dauthanhtrung/Arduino-Simple-Phone/CODE TEST/KeyPad/KeyPad.ino

#include <Keypad.h>

const byte ROWS = 4; 
const byte COLS = 4; 

char hexaKeys[ROWS][COLS] = {
  {'1', '2', '3', 'A'},
  {'4', '5', '6', 'B'},
  {'7', '8', '9', 'C'},
  {'*', '0', '#', 'D'}
};

byte rowPins[ROWS] = {9, 10, 11, 12}; 
byte colPins[COLS] = {A0, A1, A2, A3}; 

Keypad key = Keypad(makeKeymap(hexaKeys), rowPins, colPins, ROWS, COLS); 

void setup(){
  Serial.begin(9600);
}
  
void loop(){
  char customKey = key.getKey();
  
  if (customKey){
    Serial.println(customKey);
  }
}
